JoanSanbartolome/Proyecto_DCI/outputs/SPI_Advanced_Implementation.md

# SPI Advanced Implementation: STM32F746ZG

This document provides advanced hardware and software tuning recommendations for high-speed SPI interfaces.

## 🚀 High-Speed Tuning
- **GPIO Speed:** Set `OSPEEDR` register to `11` (Very High Speed) for SCK and MOSI pins when operating above 25 MHz to maintain sharp clock edges.
- **Slew Rate Control:** If traces are very short (< 20mm), a 'Medium' speed setting may be used to reduce radiated EMI while still meeting timing requirements.

## 🔗 Multi-Slave Management
- **Topology:** Use a **Star Topology** for SCK, MISO, and MOSI lines when connecting both the onboard Flash and the expansion header.
- **NSS Strategy:** Prefer **Software NSS management** using standard GPIOs for Chip Select. This avoids the limitations of the hardware NSS pin and allows for more than one slave on the same peripheral.
- **MISO Contention:** Ensure that any external devices connected to the GPIO header have high-impedance (tri-state) MISO outputs when their specific Chip Select is inactive.

## 🛡 Industrial Robustness
- **Filtering:** For signals traveling to the expansion header, consider adding **10-47 pF capacitors** to ground on the SCK line at the receiver end to filter high-frequency transients.
- **Isolation:** If the SPI bus is intended to interface with external high-voltage equipment, use a digital isolator (e.g., ISO7741) to provide galvanic isolation.

[Source: stm32f746zg.pdf, Best Practices for Embedded Design]
