JoanSanbartolome/Proyecto_DCI/fabricacion/Report Board Stack/STM32_PCB.xls

Board Stack Report
Stack Up |  | Layer Stack
Layer | Board Layer Stack | Name | Material | Thickness | Constant | Color
1 |  | Top Overlay |  | 0mm
2 |  | Top Solder | SM-001 | 0.0254mm | 4 | #FF008000
3 |  | Top Surface Finish | Gold | 0.004mm |  | #FFFFB200
4 |  | Top Layer | CF-004 | 0.0175mm
5 |  | Dielectric 1 | PP-004 | 0.06604mm | 3.8
6 |  | Dielectric 2 | PP-006 | 0.07112mm | 4.1
7 |  | Int1 (GND) | CF-004 | 0.035mm
8 |  | Dielectric 3 | Core-039 | 1.1mm | 4.8
9 |  | Int2 (PWR) | CF-004 | 0.035mm
10 |  | Dielectric 4 | PP-006 | 0.07112mm | 4.1
11 |  | Dielectric 5 | PP-004 | 0.06604mm | 3.8
12 |  | Bottom Layer | CF-004 | 0.0175mm
13 |  | Bottom Surface Finish | Gold | 0.004mm |  | #FFFFB200
14 |  | Bottom Solder | SM-001 | 0.0254mm | 4 | #FF008000
15 |  | Bottom Overlay |  | 0mm
 | Height : 1.53812mm
