JoanSanbartolome/Proyecto_DCI/informe/Imagenes/armónicos.png

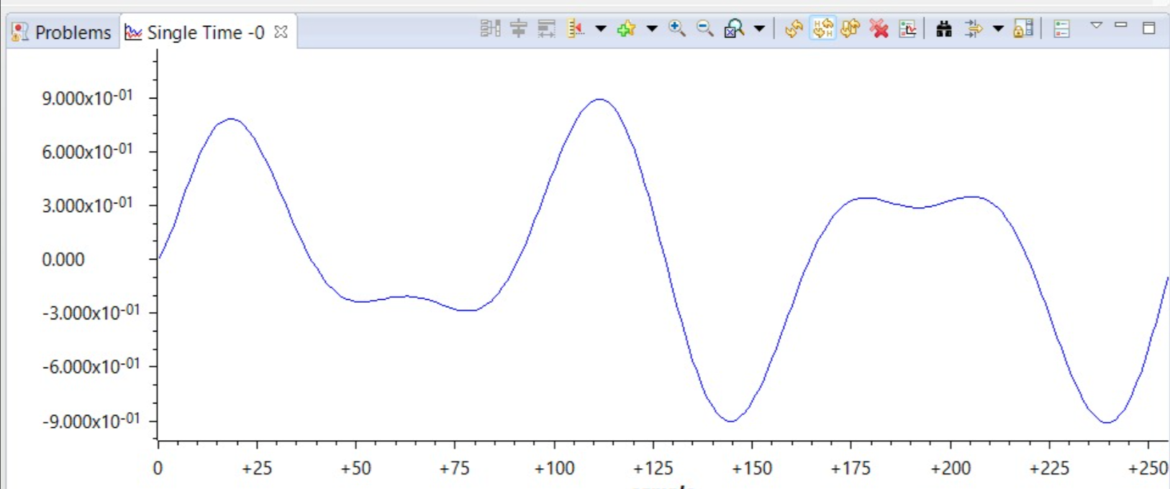
informe/Imagenes/armónicos.png
