JoanSanbartolome/Proyecto_DCI/informe/Imagenes/diffPair_USB.png

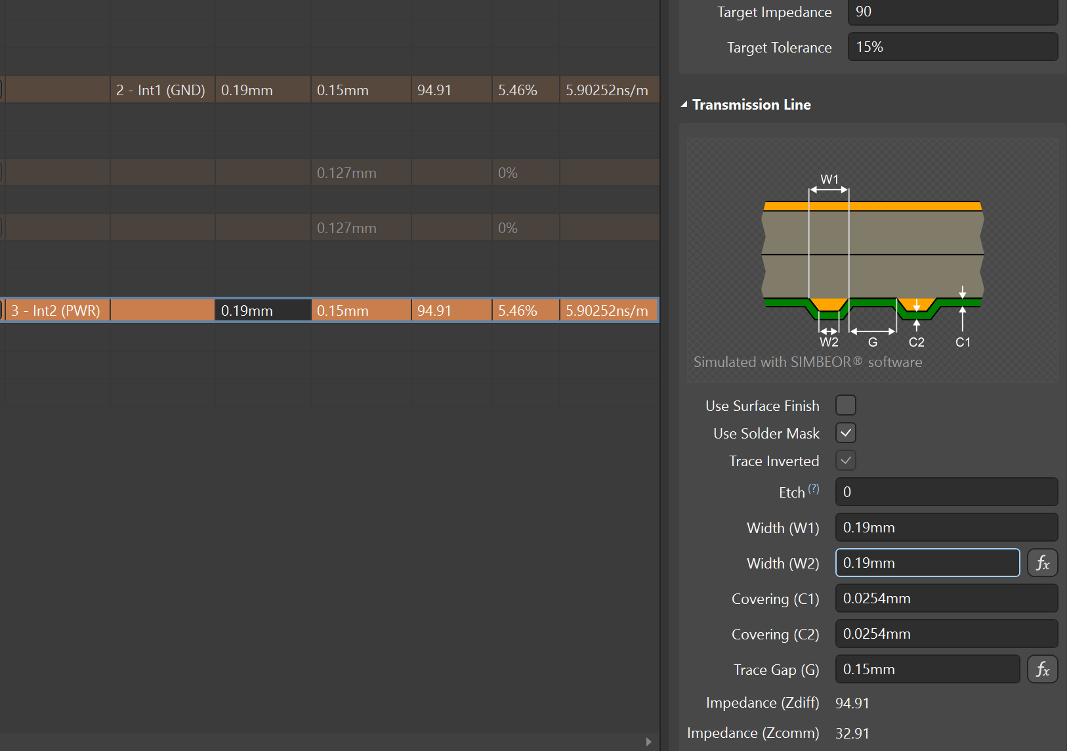
informe/Imagenes/diffPair_USB.png
