JoanSanbartolome/Proyecto_DCI/informe/Imagenes/Ethernet.png

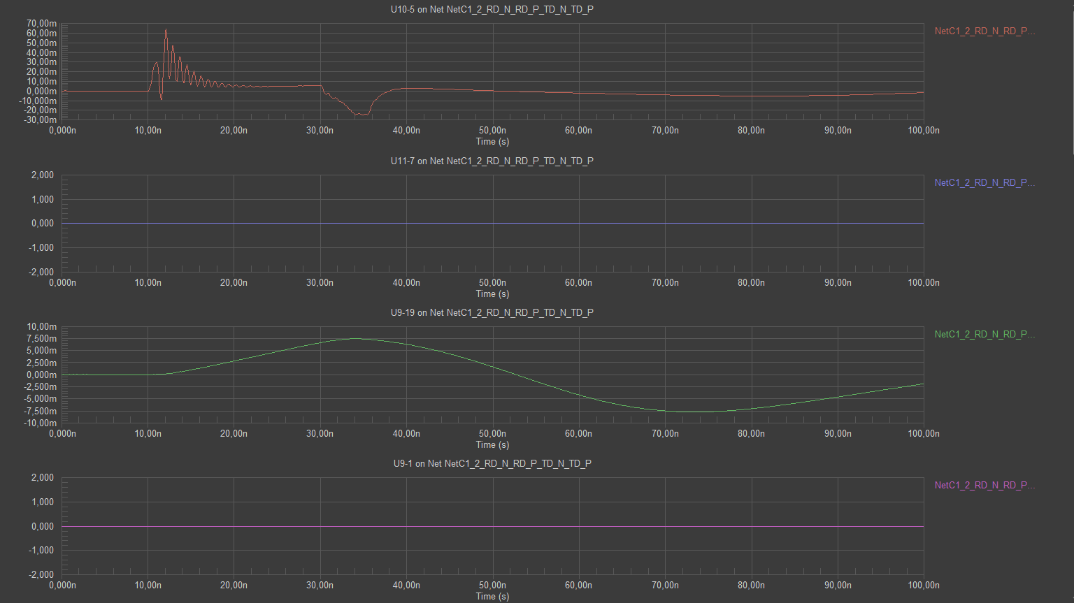
informe/Imagenes/Ethernet.png
