JoanSanbartolome/Proyecto_DCI/informe/Imagenes/flujogramab.png

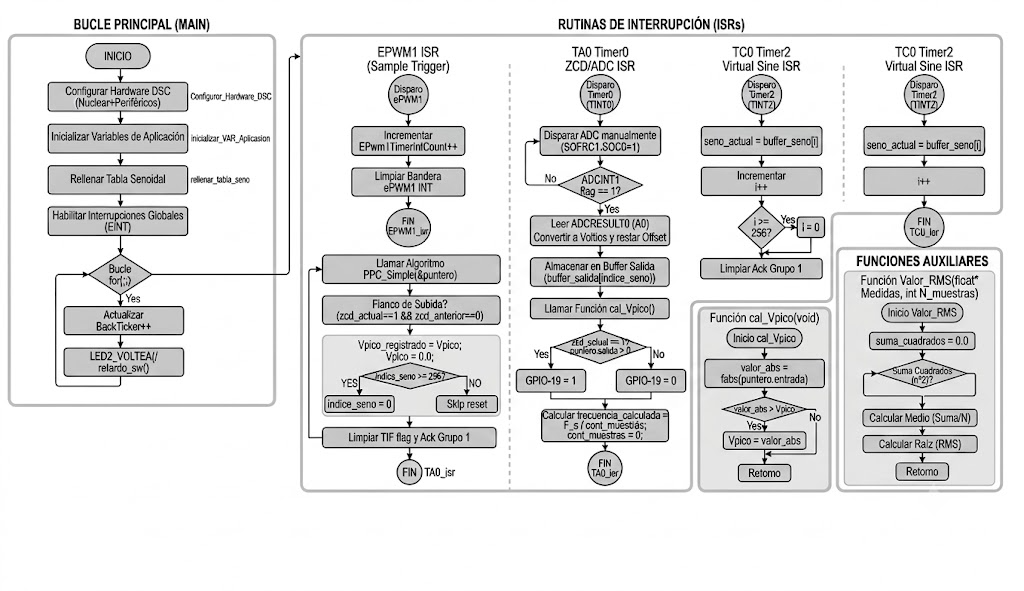
informe/Imagenes/flujogramab.png
