JoanSanbartolome/Proyecto_DCI/informe/Imagenes/pasoporceo2.png

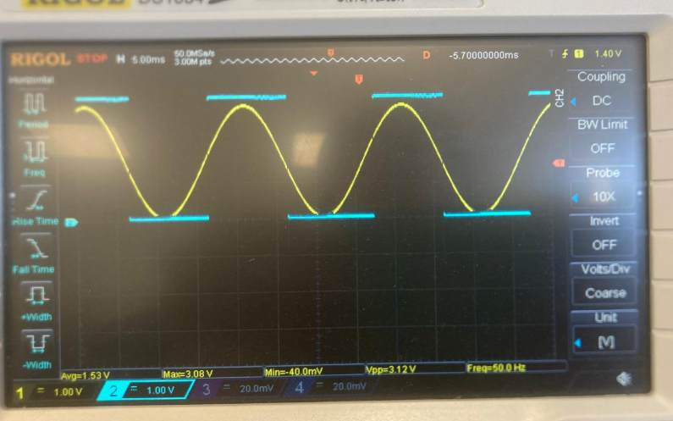
informe/Imagenes/pasoporceo2.png
