JoanSanbartolome/Proyecto_DCI/informe/Imagenes/salida_PA_200HZ.png

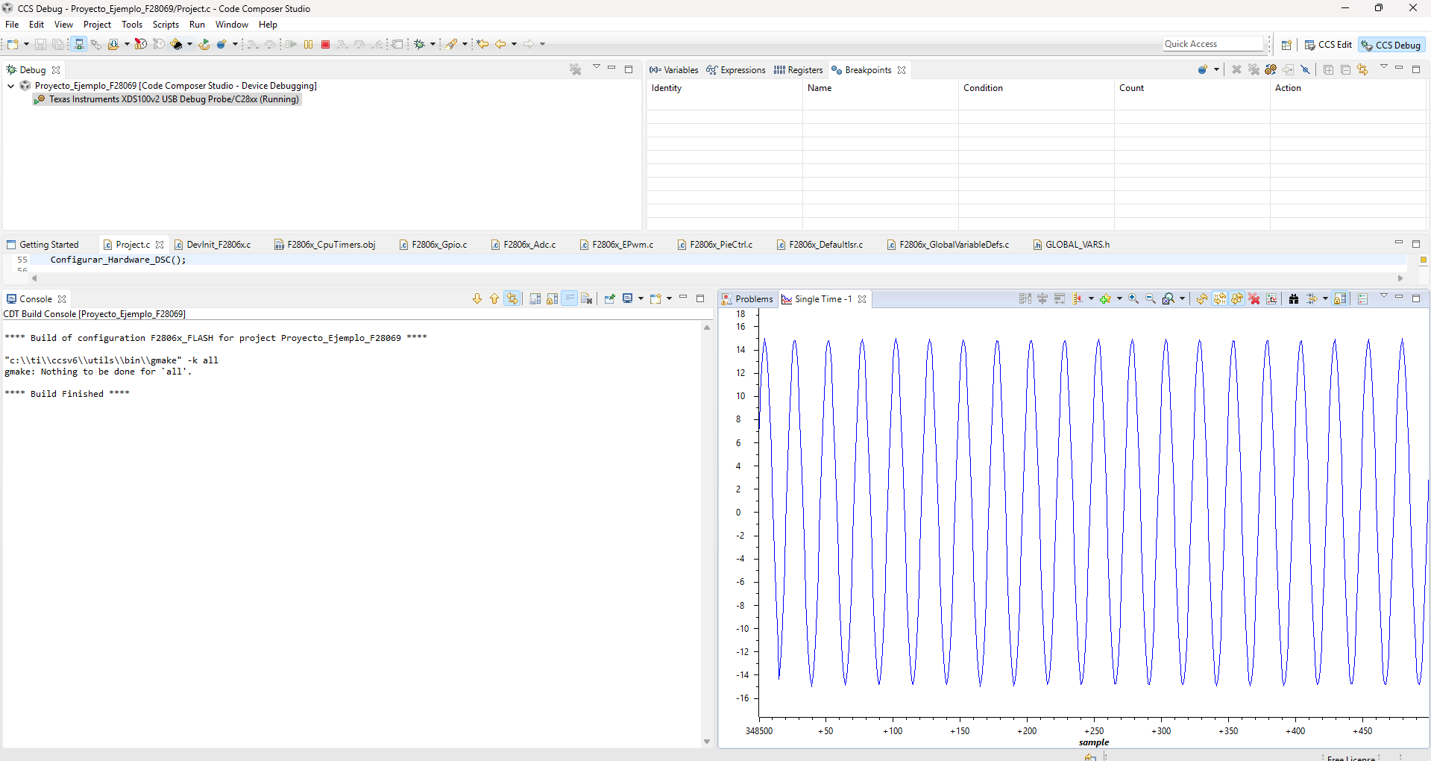
informe/Imagenes/salida_PA_200HZ.png
