JoanSanbartolome/Proyecto_DCI/informe/Imagenes/semiciclos.png

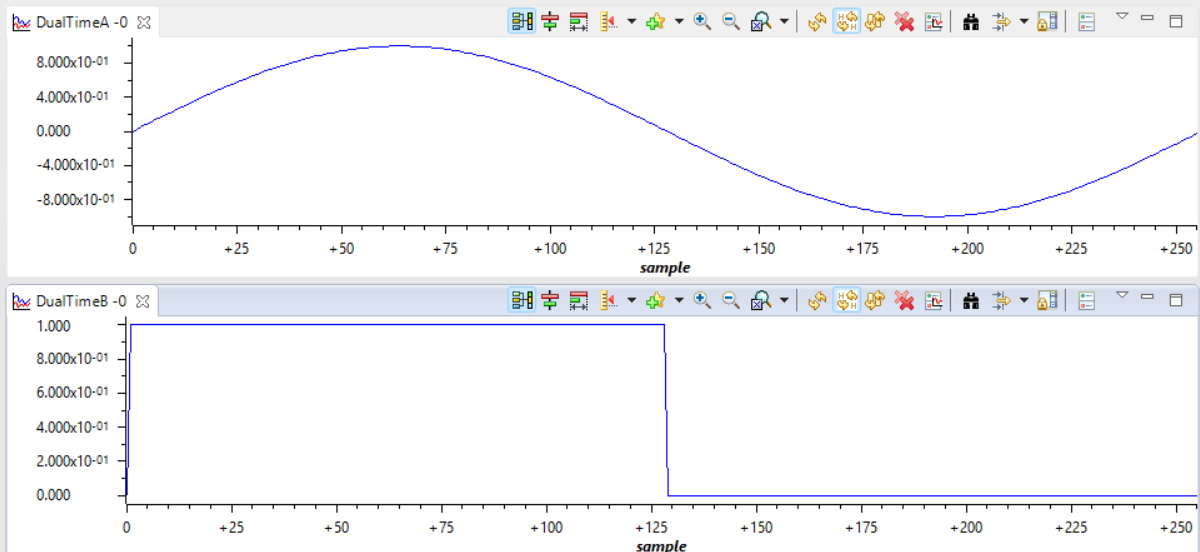
informe/Imagenes/semiciclos.png
