JoanSanbartolome/Proyecto_DCI/informe/Imagenes/WhatsApp Image 2026-05-16 at 17.02.07.jpeg

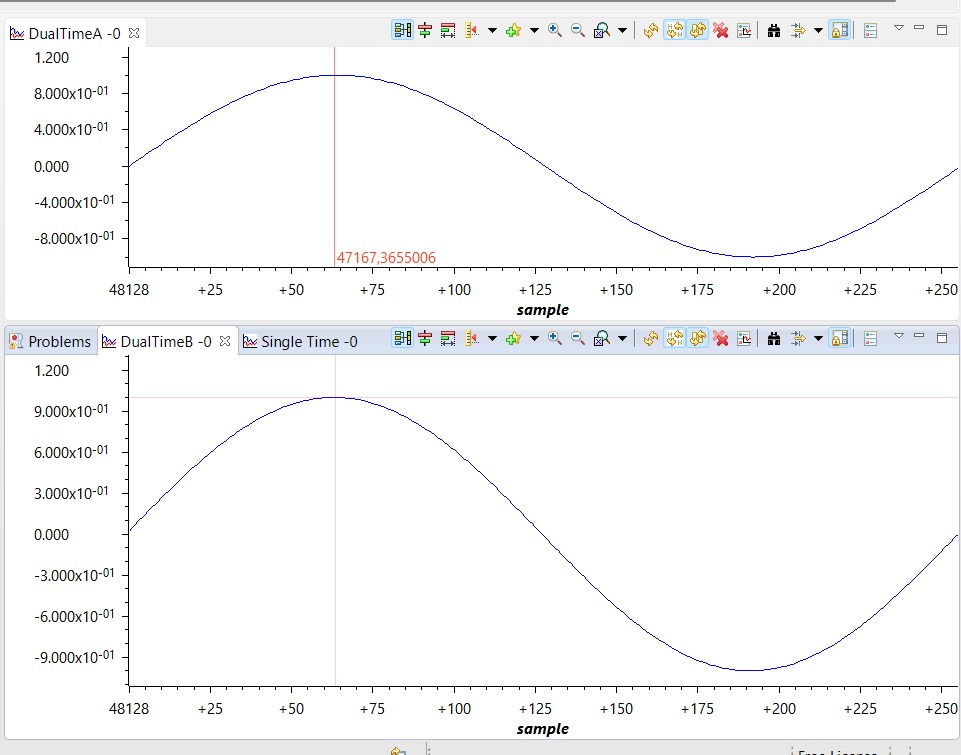
informe/Imagenes/WhatsApp Image 2026-05-16 at 17.02.07.jpeg
