JoanSanbartolome/Proyecto_DCI/informe/Imagenes/WhatsApp Image 2026-05-18 at 15.38.39.jpeg

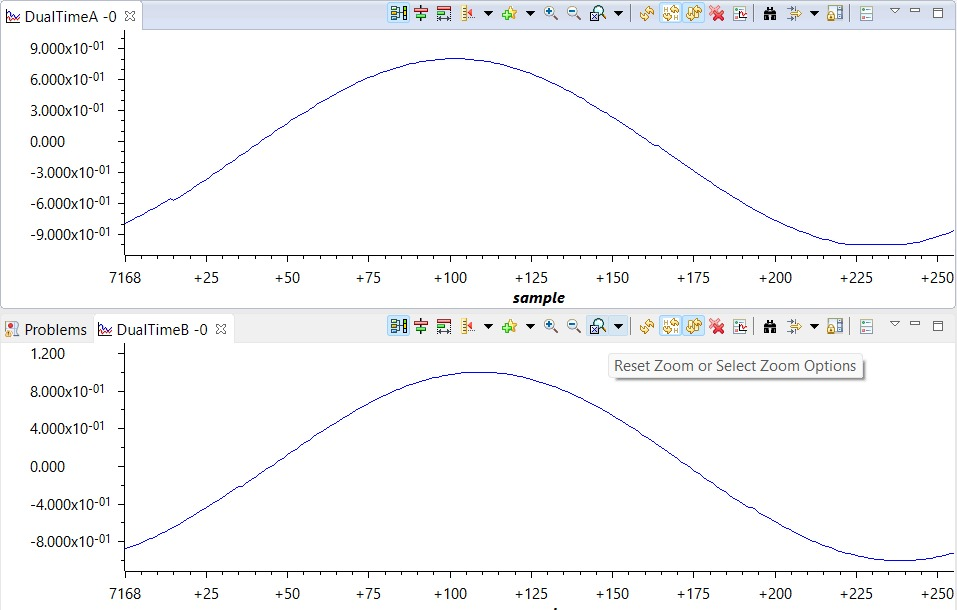
informe/Imagenes/WhatsApp Image 2026-05-18 at 15.38.39.jpeg
